willbearfruits/esp32-s3-supermini-kit/images/esp32sms3.jpeg

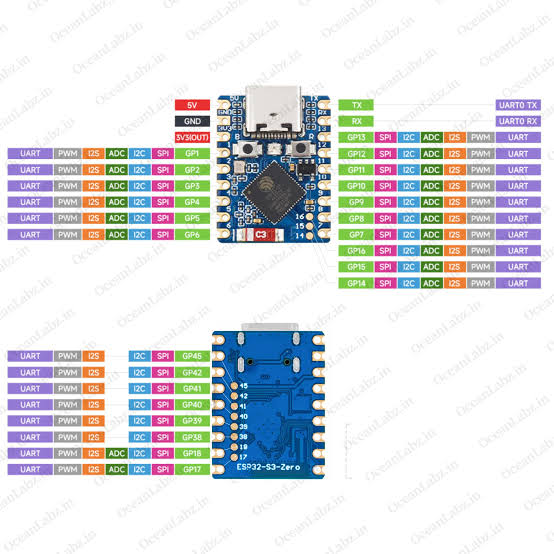
images/esp32sms3.jpeg
