willbearfruits/esp32-s3-supermini-kit/parts/research-2026-09-09/ALPS-RKJXV1224005-dimensions.gif

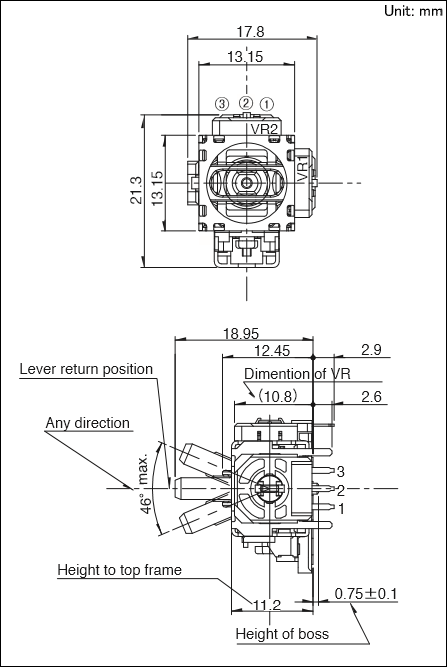
parts/research-2026-09-09/ALPS-RKJXV1224005-dimensions.gif
