willbearfruits/esp32-s3-supermini-kit/parts/research-2026-09-09/Waveshare-ESP32-S3-Zero-dimensions.jpg

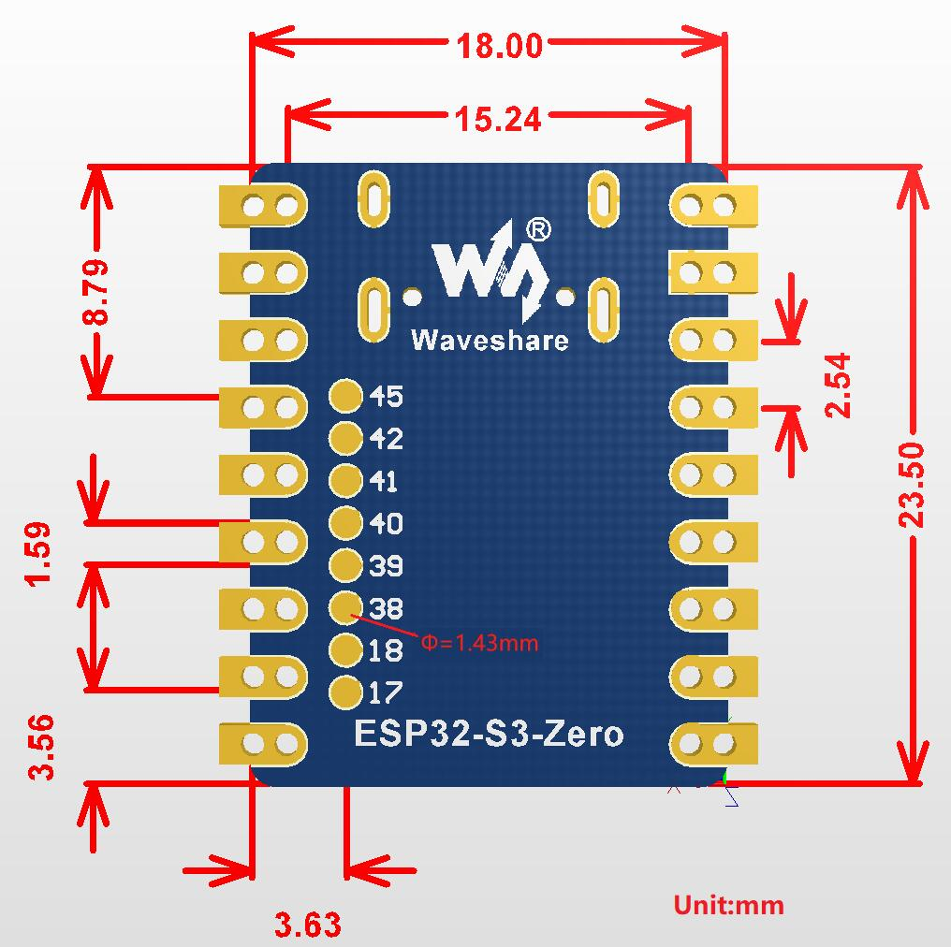
parts/research-2026-09-09/Waveshare-ESP32-S3-Zero-dimensions.jpg
