willbearfruits/esp32-s3-supermini-kit/docs/assembly/assets/controls.png

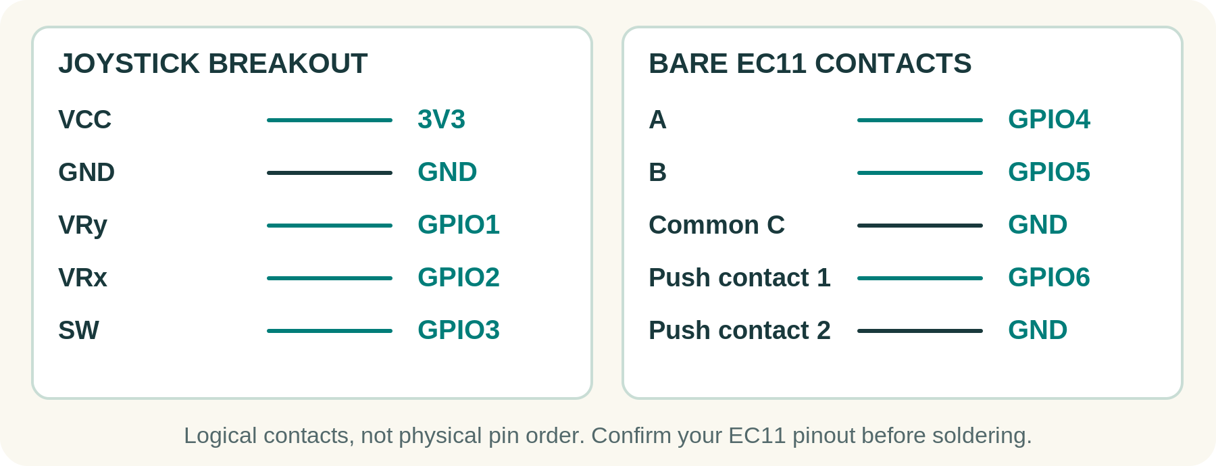
docs/assembly/assets/controls.png
