willbearfruits/esp32-s3-supermini-kit/docs/assembly/assets/dac.png

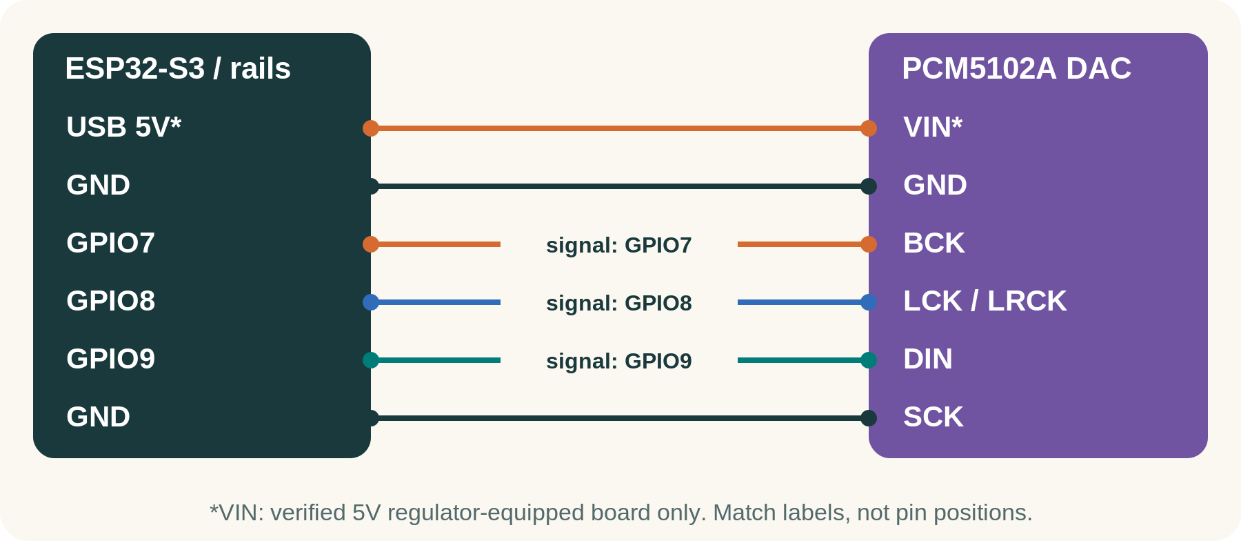
docs/assembly/assets/dac.png
