willbearfruits/esp32-s3-supermini-kit/docs/assembly/assets/hero.png

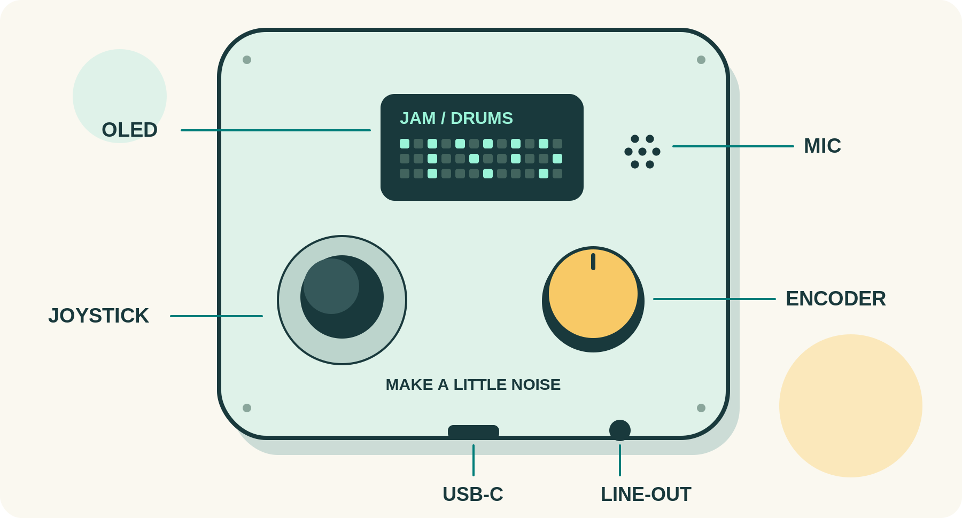
docs/assembly/assets/hero.png
