willbearfruits/esp32-s3-supermini-kit/docs/assembly/assets/placement.png

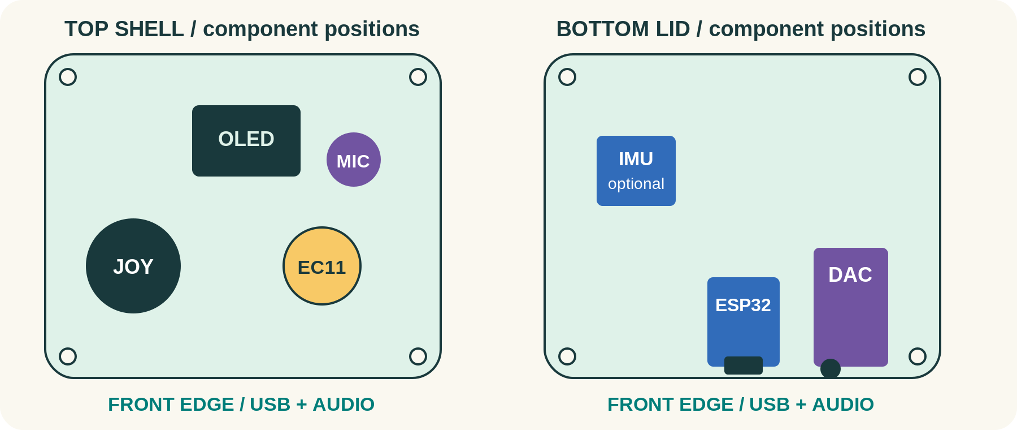
docs/assembly/assets/placement.png
