willbearfruits/esp32-s3-supermini-kit/docs/assembly/assets/power.png

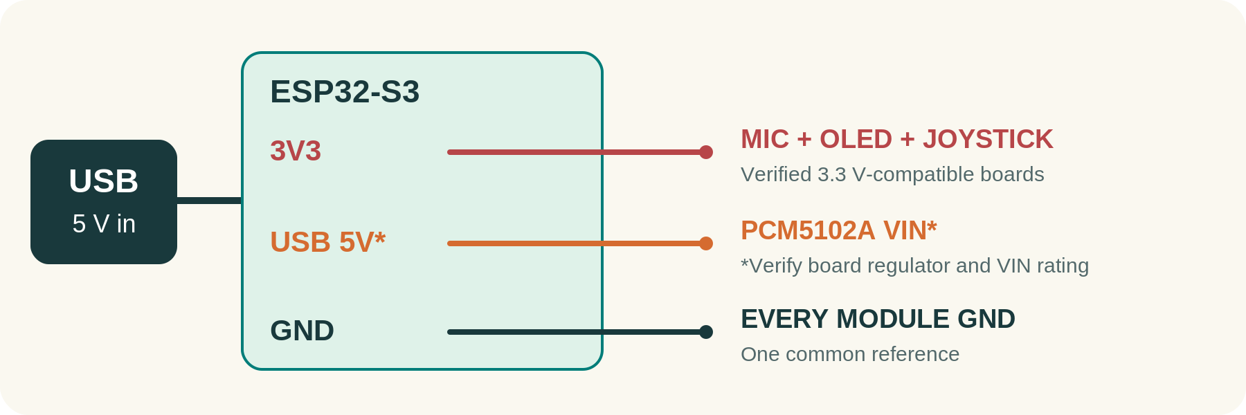
docs/assembly/assets/power.png
