willbearfruits/esp32-s3-supermini-kit/docs/wiring.png

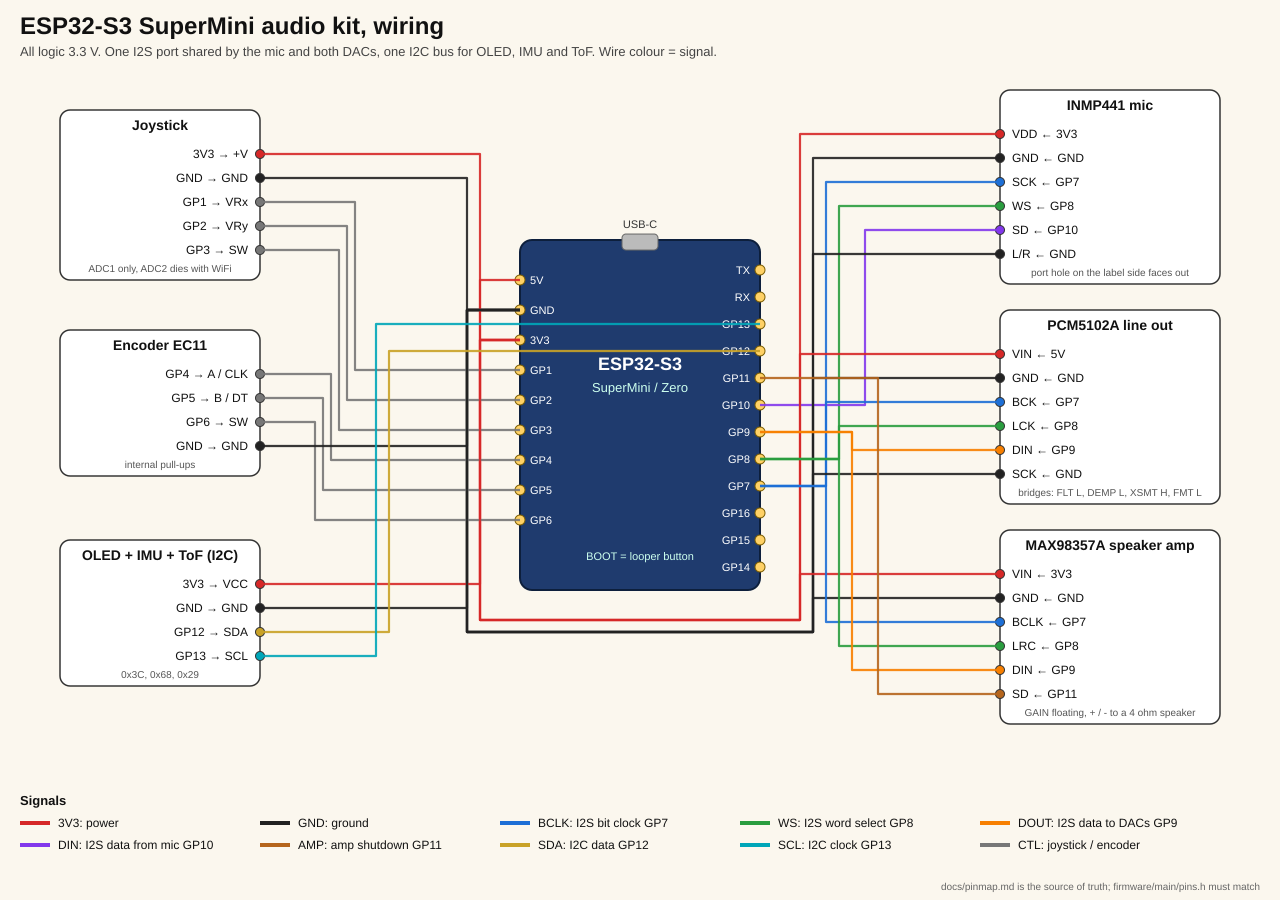
docs/wiring.png
