willbearfruits/esp32-s3-supermini-kit/enclosure/out/assembled.png

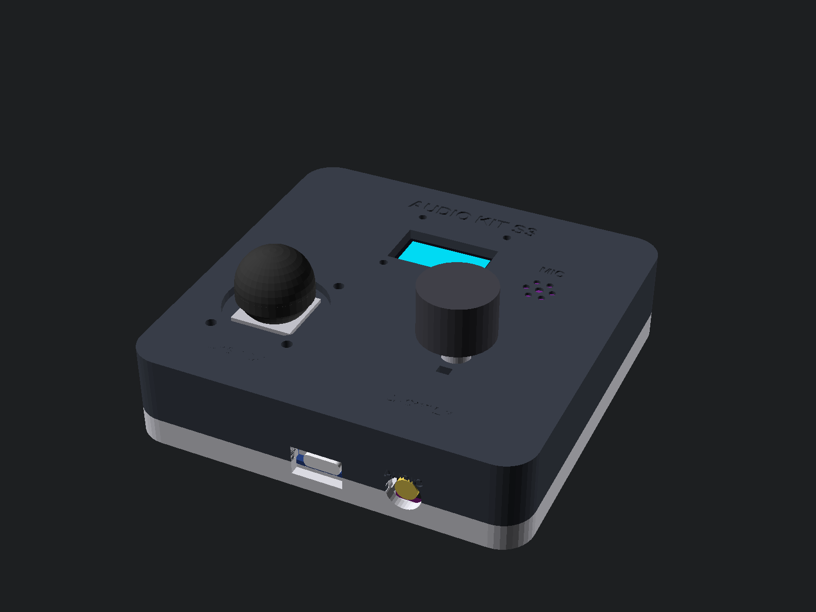
enclosure/out/assembled.png
