willbearfruits/esp32-s3-supermini-kit/firmware/main/tune.h

// Hyperpop autotune: hard, instant snap of the voice to the scale, with an
// octave-up double and some drive.
#pragma once
#include "voice.h"
#include "scale.h"

enum { TUNE_HARD, TUNE_HARMONY, TUNE_ROBOT, TUNE_RAW, TUNE_N };
void tune_init(void);
void tune_set_mode(int mode);
const char *tune_mode_name(int mode);
void tune_process(const float *in, float *out, int n, const voice_t *v, const scale_t *sc);
int  tune_target(void);   // MIDI note currently tuned to, -1 when none
