willbearfruits/esp32-s3-supermini-kit/firmware/main/imu.h

// MPU6050 tilt sensing for expression. Optional; absent means zero tilt.
#pragma once
#include <stdbool.h>
#include "driver/i2c_master.h"
bool imu_init(i2c_master_bus_handle_t bus);
bool imu_present(void);
void imu_poll(float *roll_deg, float *pitch_deg);   // filtered, call at 50 Hz or so
